Owen-Ball/LCR_Meter/CAD/menu_assembly/menu_assembly.SLDASM

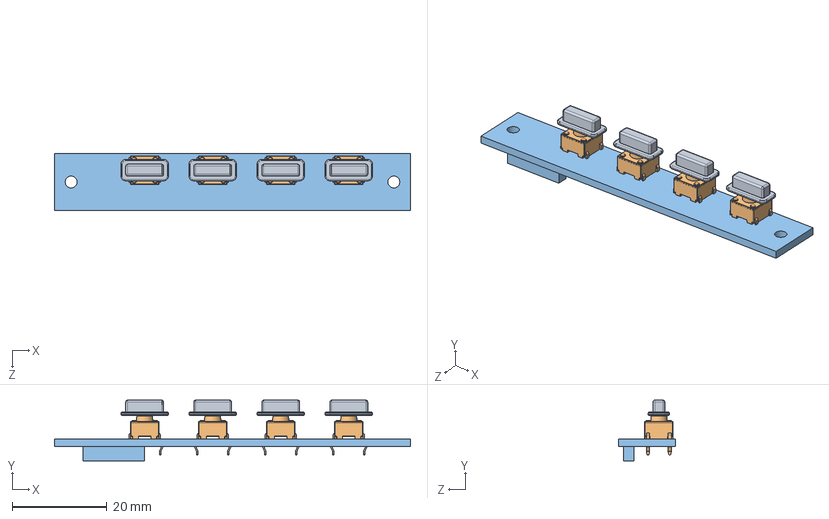
[picture p3: CAD file, 2026-08-15]
CAD/menu_assembly/menu_assembly.SLDASM
75.0 x 12.8 x 12.0 mm
menu_PCB
tactileswitch-short x 4
menu_buttons x 4
