Owen-Ball/LCR_Meter/CAD/selector_assembly/selector_assembly.SLDASM

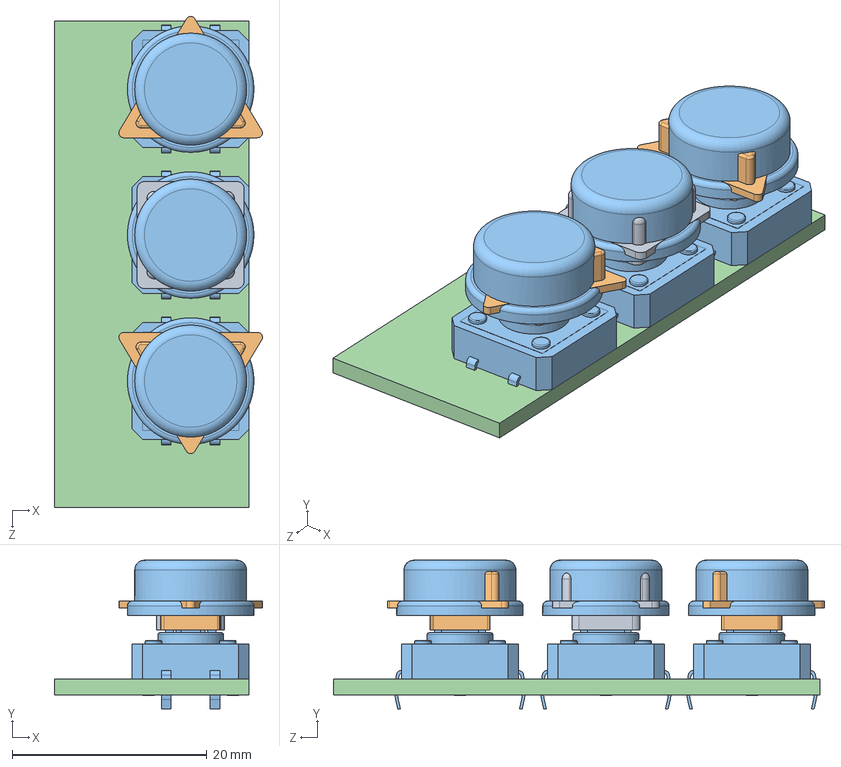
[picture p4: CAD file, 2026-09-21]
CAD/selector_assembly/selector_assembly.SLDASM
21.4 x 15.3 x 50.5 mm
pcb
button x 3
arrow_cap x 2
enter_cap
