Owen-Ball/LCR_Meter/CAD/m3_spacer.SLDPRT

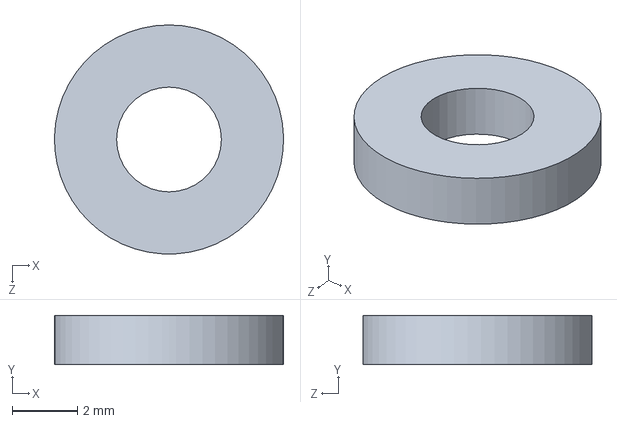
[picture p19: CAD file, 2026-09-24]
CAD/m3_spacer.SLDPRT
7.00 x 1.50 x 7.00 mm
