Owen-Ball/LCR_Meter/CAD/menu_assembly/tactileswitch-short.SLDPRT

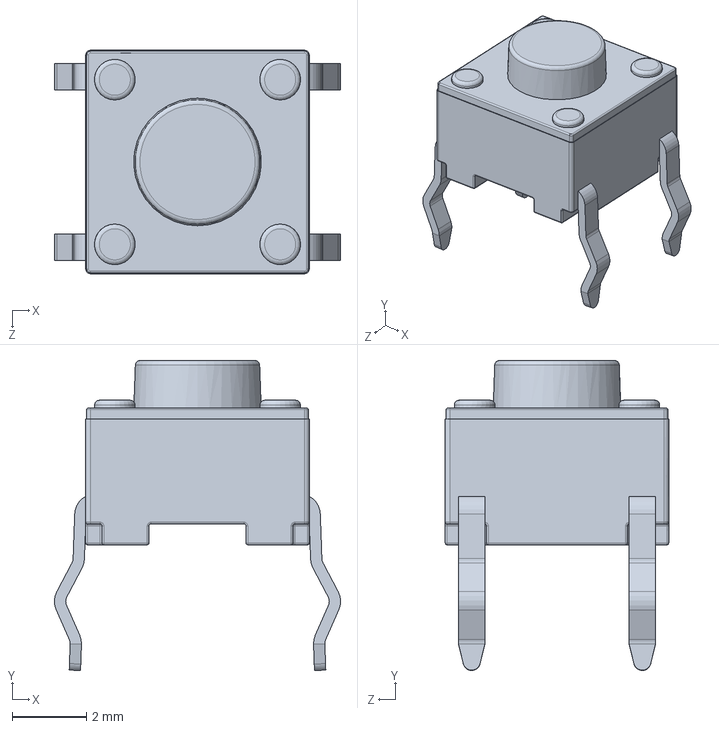
[picture p20: CAD file, 2026-08-01]
CAD/menu_assembly/tactileswitch-short.SLDPRT
7.69 x 8.33 x 6.01 mm
