Owen-Ball/LCR_Meter/CAD/selector_assembly/pcb.SLDPRT

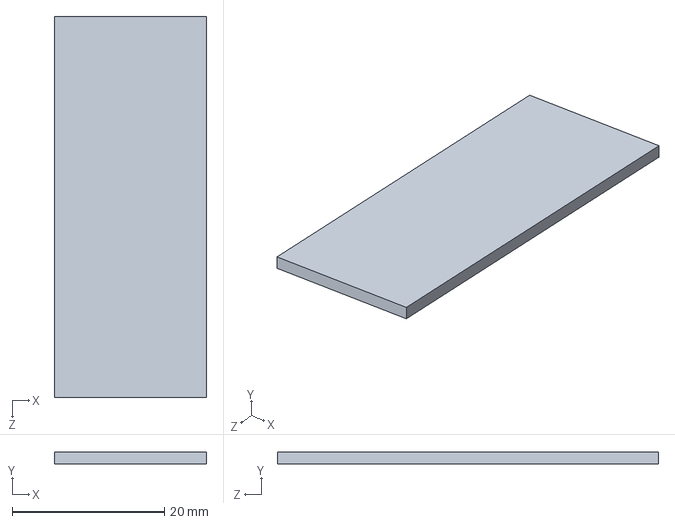
[picture p21: CAD file, 2026-08-11]
CAD/selector_assembly/pcb.SLDPRT
20.0 x 1.60 x 50.0 mm
