Owen-Ball/LCR_Meter/CAD/STLs/front_panel3.DXF

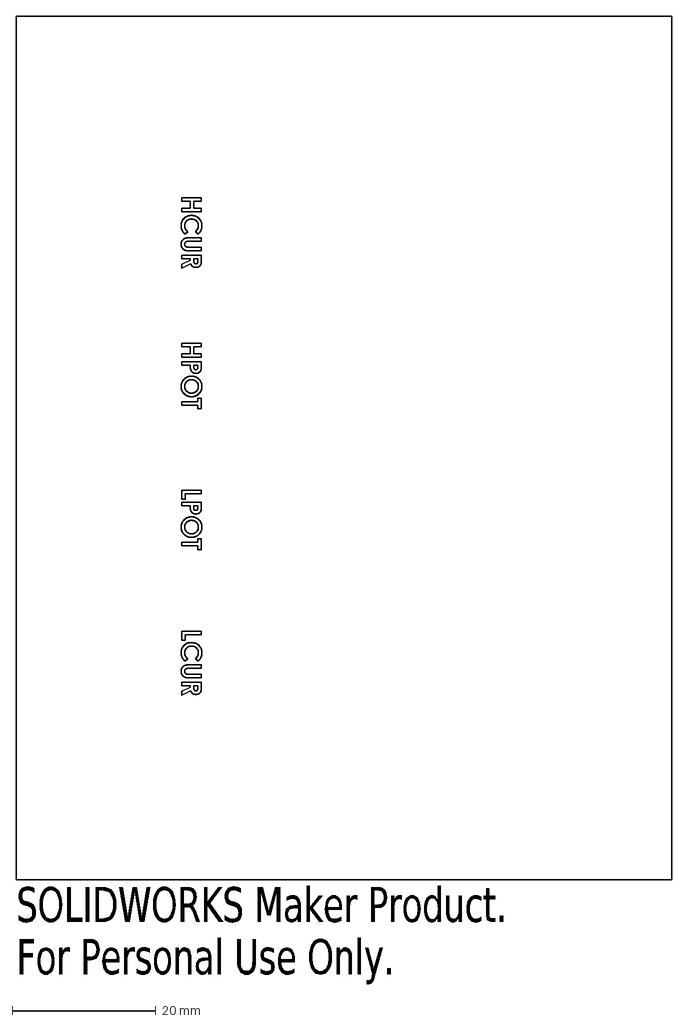
[picture p22: CAD file, 2026-09-24]
CAD/STLs/front_panel3.DXF
SOLIDWORKS Maker Product.
For Personal Use Only.
