Owen-Ball/LCR_Meter/CAD/compartment_lid.SLDPRT

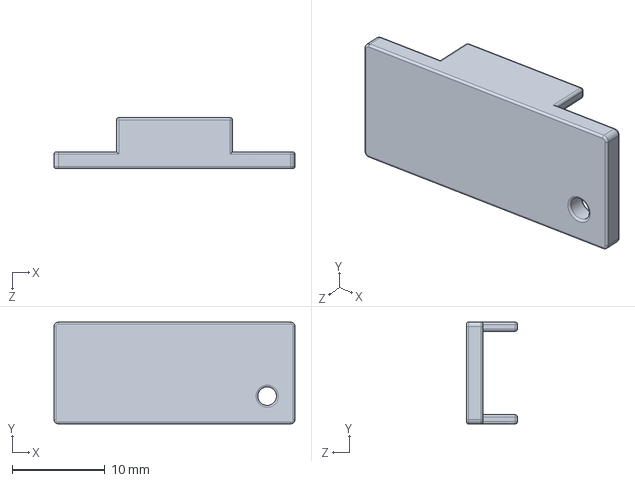
[picture p23: CAD file, 2026-09-24]
CAD/compartment_lid.SLDPRT
26.0 x 11.0 x 5.50 mm
