Owen-Ball/LCR_Meter/CAD/selector_assembly/button.SLDPRT

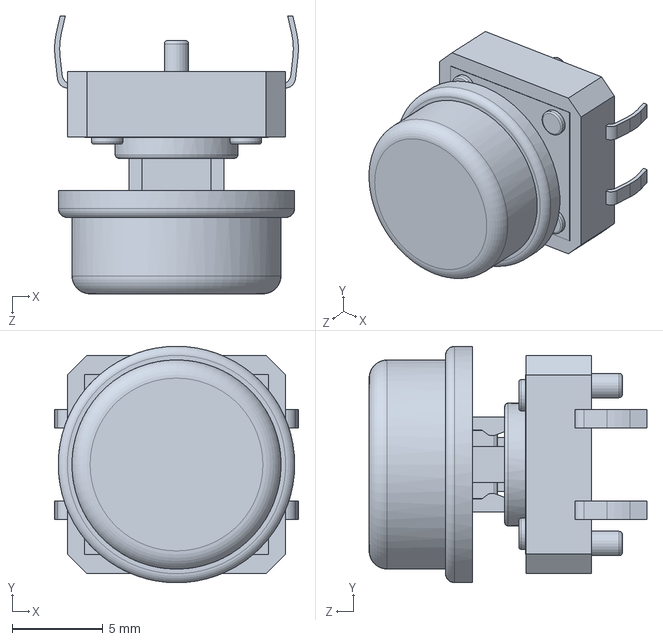
[picture p24: CAD file, 2026-08-02]
CAD/selector_assembly/button.SLDPRT
13.4 x 13.0 x 15.3 mm
