Owen-Ball/LCR_Meter/CAD/STLs/enter_cap - arrow_cap-1.STL

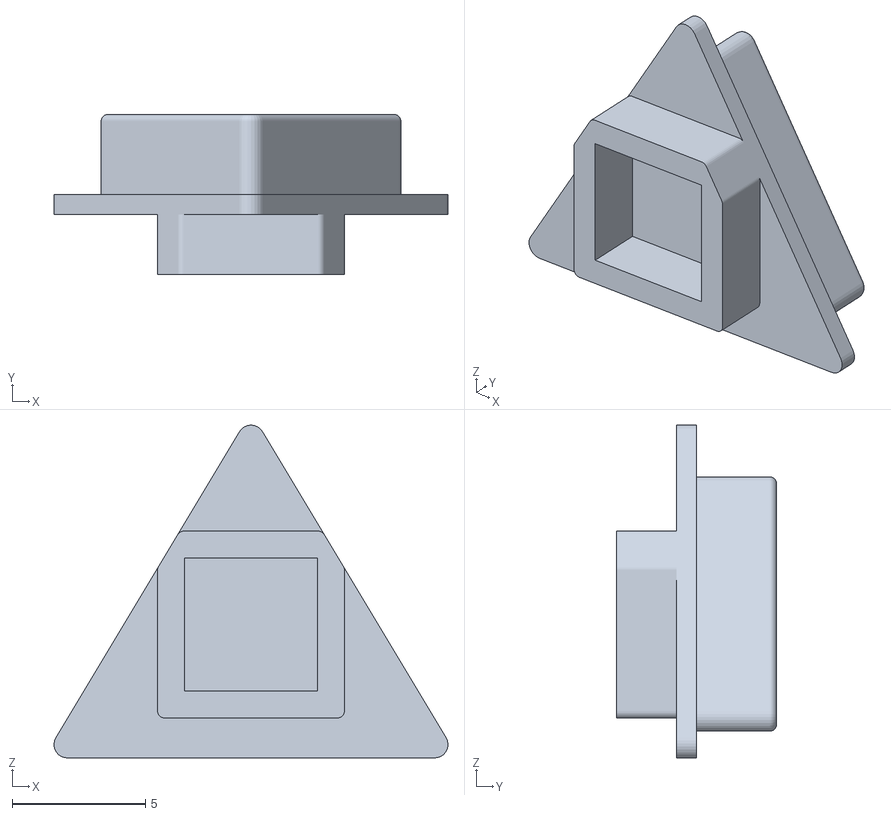
[picture p25: CAD file, 2026-09-21]
CAD/STLs/enter_cap - arrow_cap-1.STL
14.8 x 6.00 x 12.5
