Owen-Ball/LCR_Meter/CAD/STLs/enter_cap - button-1.STL

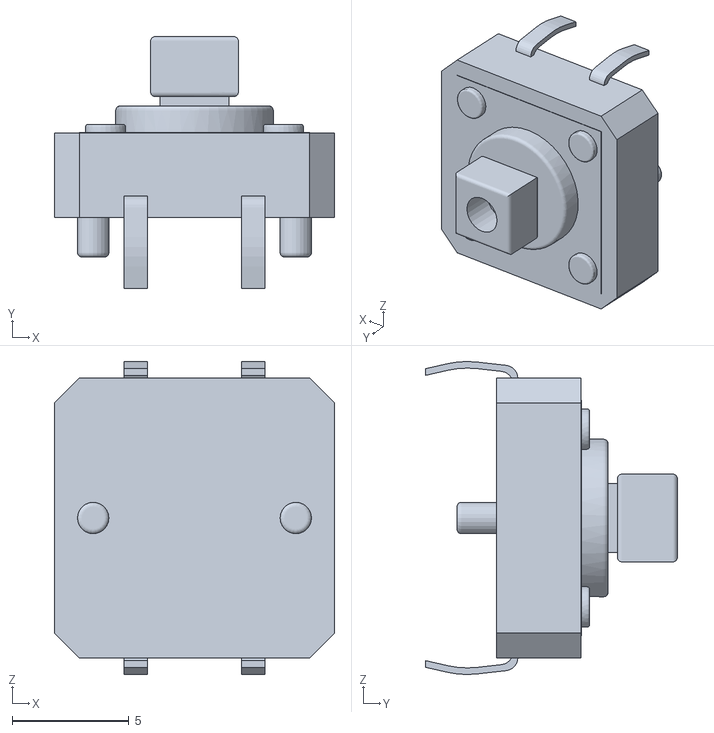
[picture p26: CAD file, 2026-09-21]
CAD/STLs/enter_cap - button-1.STL
12.0 x 10.8 x 13.4
