Owen-Ball/LCR_Meter/CAD/back_panel.SLDPRT

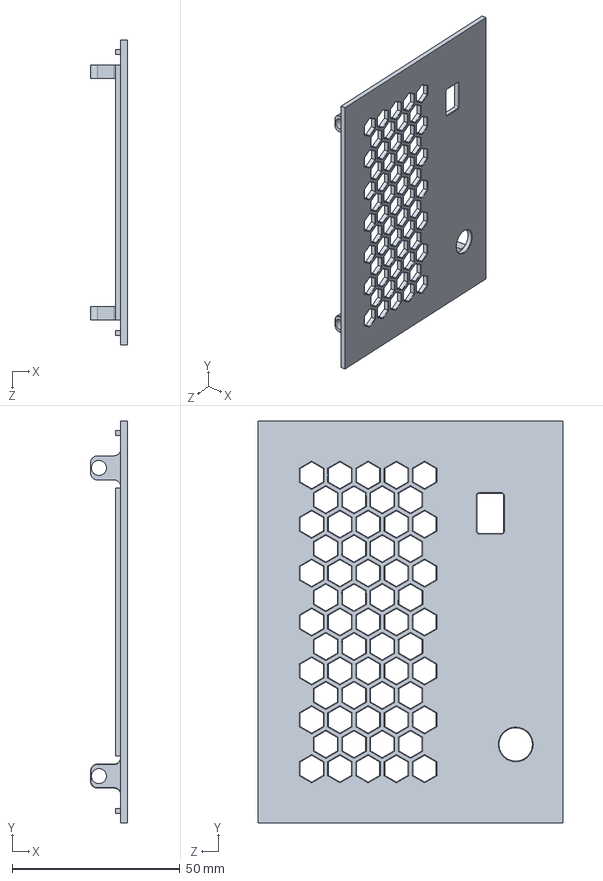
[picture p27: CAD file, 2026-09-18]
CAD/back_panel.SLDPRT
11.0 x 120.0 x 91.0 mm
