Owen-Ball/LCR_Meter/CAD/STLs/enter_cap - pcb-1.STL

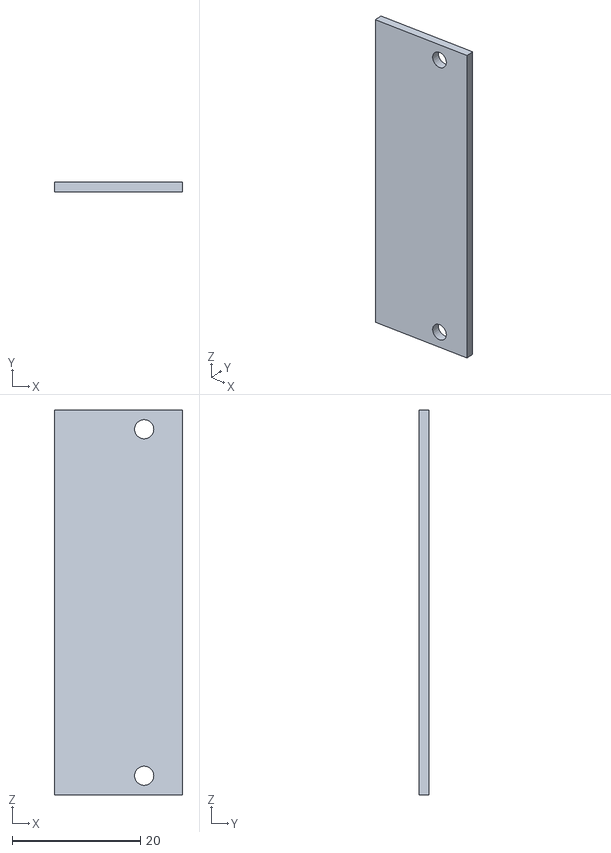
[picture p28: CAD file, 2026-09-21]
CAD/STLs/enter_cap - pcb-1.STL
20.0 x 1.60 x 60.0
