Owen-Ball/LCR_Meter/CAD/TFT_glass.SLDPRT

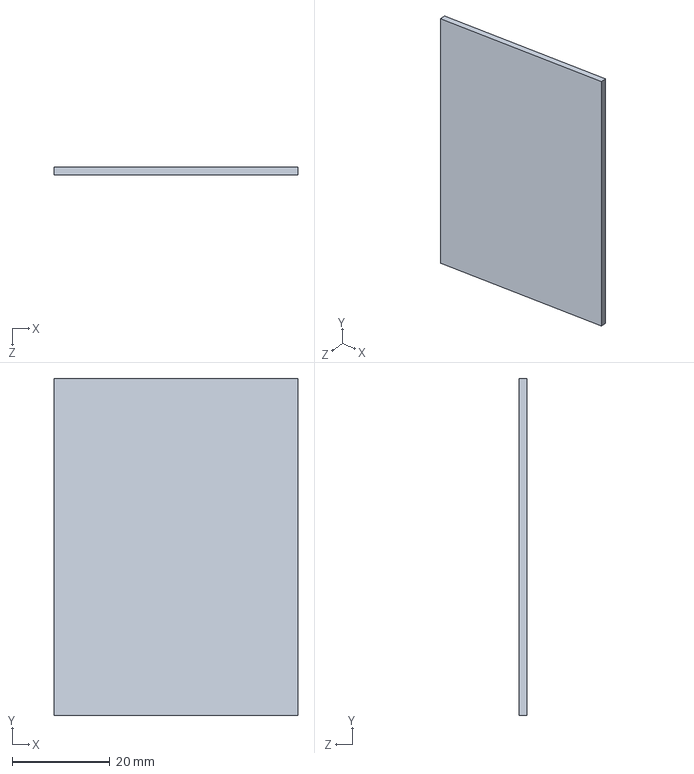
[picture p29: CAD file, 2026-08-01]
CAD/TFT_glass.SLDPRT
50.0 x 69.0 x 1.68 mm
