Owen-Ball/LCR_Meter/CAD/2.8 TFT Module.stp

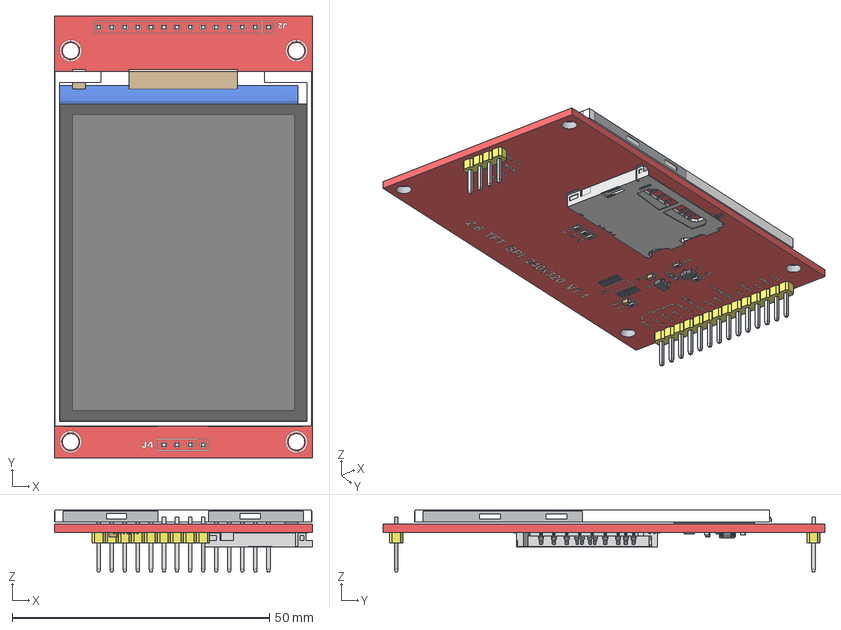
[picture p30: CAD file, 2026-08-01]
CAD/2.8 TFT Module.stp
50.2 x 85.9 x 12.0 mm
2.8 LCD TFT Module - Without Glass
0603 Resistor x 6
0603 Capacitor x 2
SOT23-3 x 2
2.8in TFT(Without Glass)- Tucked Cable
