Owen-Ball/LCR_Meter/CAD/TFT_2p8.step

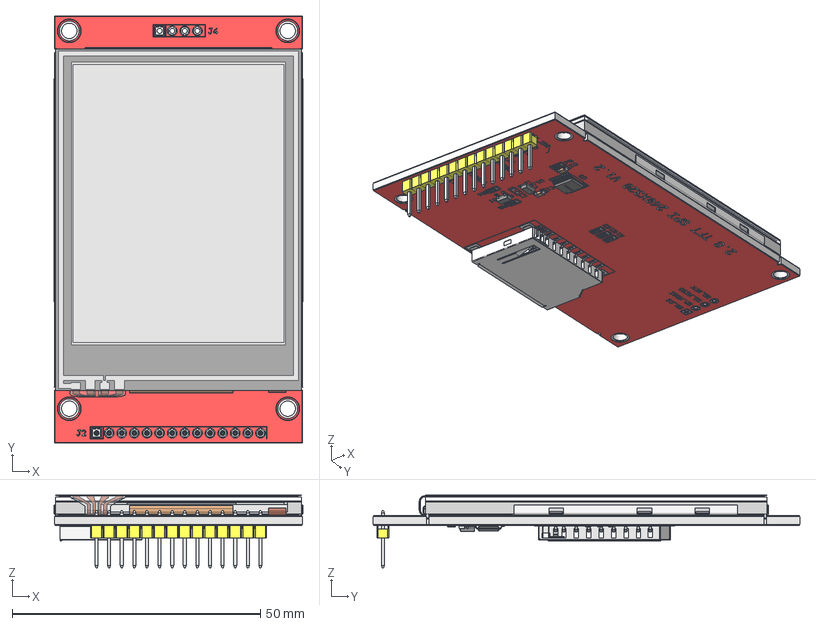
[picture p31: CAD file, 2026-07-29]
CAD/TFT_2p8.step
50.1 x 86.0 x 14.6 mm
plate and holes
circle001
circle002
circle003
circle004
border001
border002
ShapeString099
ShapeString100
ShapeString102
ShapeString103
cupper_upper
cupper_bottom
mask_bottom
res_silk
res_silk001
res_silk002
res_silk003
res_silk004
res_silk005
cap_silk_up
cap_silk_dwn
cap_silk_up001
cap_silk_dwn001
sot23_left
sot23_right
sot23_left001
sot23_right001
u2_silk002
sd_silk001
line_silk001
line_silk002
ShapeString067
ShapeString105
ShapeString106
ShapeString107
ShapeString108
ShapeString068
ShapeString110
ShapeString111
ShapeString112
ShapeString113
ShapeString069
ShapeString115
ShapeString116
ShapeString117
ShapeString070
ShapeString119
ShapeString120
ShapeString121
ShapeString122
ShapeString071
ShapeString124
ShapeString125
ShapeString126
ShapeString073
ShapeString128
ShapeString129
ShapeString130
ShapeString131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
