Owen-Ball/LCR_Meter/simulation/full_design/dac_filter.asc

C1: cap; 100p
C2: cap; 220p
C3: cap; 100p
R1: res; 10k
R2: res; 8.2k
R3: res; 10k
R4: res; 10k
R5: res; 10k
R6: res; 8.2k
U1: opamp2; tlv916x
Named nets: VCM, VP, VN, VOUT, VSS, VDD
