Owen-Ball/LCR_Meter/simulation/full_design/tb_dac_filter.asc

V1: voltage; SINE(0 1 50000); AC .61
V2: voltage; SINE(0 1 50000); AC .61
V3: voltage; 5
V4: voltage; 0
V5: voltage; 2.5
X1: dac_filter
Named nets: VCM, 0, VSS, VDD
.include tlv916x.txt
.ac dec 20 10 10Meg
