Owen-Ball/LCR_Meter/simulation/full_design/pga.asc

C1: cap; 470p
C2: cap; 470p
C3: cap; 2.7n
C4: cap; 100n
C5: cap; 2p
C6: cap; 2p
R1: res; 8.2k
R2: res; 1.6k
R3: res; 300
R4: res; 100
R5: res; 8.2k
R6: res; 1.6k
R7: res; 300
R8: res; 100
R9: res; 10Meg
R10: res; 10Meg
R11: res; 1k
R12: res; 1k
R13: res; 22
R14: res; 22
R15: res; 1k
R16: res; 1k
U1: THS4561
U2: ADG1209
U3: opamp2; OPA365
U4: opamp2; OPA365
Named nets: VDD, VSS, VP, VN, OUTP, OUTN, A0, A1, VCM
