Owen-Ball/LCR_Meter/simulation/full_design/top_hierarchy.asc

C1: cap; 1p
C2: cap; 1p
C3: cap; 100p
C4: cap; 15p
C5: cap; 50p
C6: cap; 15p
C7: cap; 15p
C8: cap; 100p
E1: e; 1
E2: e; 1
E3: e; 1
E4: e; 1
L1: ind; 1µ; Rser=1m
R1: res; 100
R2: res; 1k
R3: res; 10k
R4: res; 100k
R5: res; 100
R6: res; 1k
R7: res; 10k
R8: res; 100k
R9: res; 1k
R10: res; 10k
R11: res; 10k
U1: opamp2; tlv916x
U2: opamp2; tlv916x
U3: opamp2; tlv916x
U4: ADG709
V1: voltage; 5
V2: voltage; 0
V3: voltage; 2.3
V6: voltage; SINE(0 1 80000); AC 1
V7: voltage; SINE(0 1 80000); AC 1
V8: voltage; 0
V9: voltage; 5
X1: pga
X2: dac_filter
X3: pga
Named nets: 0, VSS, VDD, VCM, VMID, VMID2, RSEL0, RSEL1, TIA_OUT, TIA_FB, v_sns, i_sns, i_sns_pga, VSNS, v_sns_pga
.tran 0 .1m 0 10n
.include OPA365.txt
.ac dec 50 10 10Meg
.include tlv916x.txt
