Owen-Ball/LCR_Meter/simulation/diff_ac.asc

C1: cap; 2.7n
C3: cap; 470p
C4: cap; 470p
C5: cap; 1
C6: cap; 1
E1: e; 1
R1: res; 1k
R2: res; 1k
R3: res; 1.5k
R4: res; 1.5k
R5: res; 22
R6: res; 22
R7: res; 1Meg
R8: res; 1Meg
U1: THS4561
V1: voltage; ""; AC .5
V2: voltage; ""; AC .5
V3: voltage; 2.5
V4: voltage; 5
V5: voltage; ""; AC .5
V6: voltage; ""; AC .5
Named nets: VDDA, 0, i_dut2, VCM
.param R=1k VIN=1.25 R_diffin=1m
.ac dec 10 10 100Meg
