Owen-Ball/LCR_Meter/simulation/SigGen.asc

C1: cap; 220p
C2: cap; 220p
C3: cap; 470p
C4: cap; 1
C5: cap; 1
C6: cap; 10µ
C7: cap; 50p
C8: cap; 1µ
E1: e; 1
R1: res; 10k
R2: res; 10k
R3: res; 8.2k
R4: res; 8.2k
R5: res; 1Meg
R6: res; 1Meg
R7: res; 5.1k
R8: res; 5.1k
R9: res; 10k
R10: res; 10k
R11: res; 100
R12: res; 40
U1: opamp2; tlv916x
U2: opamp2; tlv916x
V1: voltage; 5
V2: voltage; 2.3
V3: voltage; SINE(0 .5 100); AC .5
V4: voltage; SINE(0 .5 100); AC .5
V5: voltage; ""; AC .5
V6: voltage; ""; AC .5
Named nets: 0, vdd, vcm, vout, vA, vB, vloop
.include tlv916x.txt
.ac dec 10 1 1G
.tran 0 100m 0 1u
