Owen-Ball/LCR_Meter/simulation/TIA_stab.asc

C1: cap; 30p
C2: cap; 1
C3: cap; 2p
C4: cap; 40p
C5: cap; 1p
C6: cap; 10p
C7: cap; 10p
E1: e; 1
R1: res; 1Meg
R2: res; 10k
R3: res; {R}
R4: res; 100k
R5: res; 1k
R6: res; 100
U1: opamp2; tlv916x
U2: ADG709
V1: voltage; 5
V2: voltage; 0
V3: voltage; ""; AC 1
V4: voltage; 2.5
V5: voltage; 5
V6: voltage; 0
Named nets: vss, vdd, 0, vcm, v0, v1
.ac dec 10 1 1G
.param R=10000
.include tlv916x.txt
