Owen-Ball/LCR_Meter/simulation/top.asc

C3: cap; 5n
C4: cap; 5n
C5: cap; 300p
C6: cap; 330p
E1: e; 1
E2: e; 1
E3: e; 1
E4: e; 1
L1: ind; 1e-6
R1: res; 100
R2: res; {2*R}
R3: res; {R}
R4: res; {R}
R5: res; 100
R7: res; {R}
R8: res; {R}
R9: res; {50*R}
R10: res; {R}
R11: res; {50*R}
R12: res; {R_diffin}
R13: res; {R_diffin}
R14: res; {R_diffin}
R15: res; {R_diffin}
R16: res; 1k
R17: res; 1k
R18: res; 500
R19: res; 500
R20: res; 30
R21: res; 30
R22: res; 1Meg
R: res; {2*R}
U1: opamp2; TLV354
U2: opamp2; TLV354
U3: opamp2; OPA365
U4: opamp2; OPA365
U5: opamp2; OPA365
U6: opamp2; OPA365
U7: THS4561
V1: voltage; SINE(0 {VIN} 50000)
V2: voltage; SINE(0 {VIN} 50000)
V3: voltage; 5
V4: voltage; 2.5
V5: voltage; 2.5
Named nets: 0, VDDA, VCM, vsig, vout, i_dut, v_dut, VN, i_dut2, v_dutraw
.include TLV354.txt 
.include OPA365.txt
.tran 0 100u 0 10n
.param R=1k VIN=1.25 R_diffin=1m
.options gmin=1e-10
.options gshunt=1e-9
.options reltol=0.01
.options abstol=1n
