Owen-Ball/LCR_Meter/simulation/Draft2.asc

C1: cap; 2p
C2: cap; 2p
C3: cap; 10p
C4: cap; 10p
C5: cap; 100m
C6: cap; 100m
E1: e; 1
E2: e; 100
R1: res; 27k
R3: res; 100Meg
R4: res; 5.1k
R5: res; 1k
R6: res; 330
R8: res; 100Meg
R9: res; 27k
R10: res; 5.1k
R11: res; 1k
R12: res; 330
R13: res; 1k
U1: opamp2; OPA365
U3: opamp2; OPA365
U4: MAX4052A
V1: voltage; 2.5
V2: voltage; SINE(0 .01 100000); AC 0
V3: voltage; 5
V4: voltage; 2.5
V5: voltage; 0; AC 1
V7: voltage; 2.5
V8: voltage; PULSE(0 .01 50u 1n 1n 50u 100u)
V9: voltage; 2.5
V10: voltage; 0; AC 1
Named nets: Vdd, 0, vout, vin, voutn, vinn, diff, diffin
.include OPA365.txt
.ac dec 10 10 100Meg
.tran 0 100u 0 10n
