Owen-Ball/LCR_Meter/simulation/TIA_transe.asc

C1: cap; 1p
C2: cap; 2p
C3: cap; 2p
C4: cap; 30p
E1: e; 1
E2: e; 1
R2: res; {R}
R3: res; {R}
U1: opamp2; tlv916x
V1: voltage; 2.5
V2: voltage; -2.5
V4: voltage; SINE(0 {VIN} {freq})
Named nets: vss, vdd, 0, VN, isns, VP, vsns
.include tlv916x.txt
.param R=100k VIN=1 freq=75000
.tran 0 10m 0 10n
