Owen-Ball/LCR_Meter/simulation/Draft1.asc

C1: cap; 5p
E1: e; 1
E2: e; 1
R1: res; 10k
R2: res; 1Meg
R3: res; 1Meg
R4: res; 27k
R5: res; 5.1k
R6: res; 1k
R7: res; 330
R8: res; 27k
R9: res; 5.1k
R10: res; 1k
R11: res; 330
U1: TMUX1309
U2: ADA4807-4
U4: ADG1209
U5: ADA4807-4
V1: voltage; SINE(3 1 100000)
V2: voltage; 3
V3: voltage; 2
V4: voltage; 1
V5: voltage; 4
V6: voltage; 3
V7: voltage; 2
V8: voltage; 1
V9: voltage; 5
V10: voltage; 2.5
V11: voltage; SINE(0 .01 10000)
Named nets: VDDA, 0, VN, vout, vin
.tran 0 100u 0 10n
.include OPA365.txt
