Owen-Ball/LCR_Meter/firmware/LCR/lcr_func.cpp

#include "lcr_func.h"
#include "calibration.h"
#include "codec.h"
#include "autorange.h"
#include "filter.h"

MovingAverage real_avg(16);
MovingAverage imag_avg(16);

float _curr_frequency;
float _curr_amplitude;

lcr_param_t primary_lcr_param;
lcr_param_t secondary_lcr_param;

bool auto_param;

float primary_lcr_value;
float secondary_lcr_value;

float resistance_lcr_value;
float reactance_lcr_value;

lcr_param_t *lcr_param_lookup[LCR_FUNC_NUM] = {
  &lcrParamRs,
  &lcrParamRp,
  &lcrParamCs,
  &lcrParamCp,
  &lcrParamLs,
  &lcrParamLp,
  &lcrParamXs,
  &lcrParamZMag,
  &lcrParamZPhase,
  &lcrParamQ,
  &lcrParamD,
};

void setLCRFrequency(float freq) {
  loadCalibrationPoint(freq);
  codecSetOutputFrequency(freq);
  resetAverageZ();
  _curr_frequency = freq;
}

void setLCRAmplitude(float amp) {
  float scaled_amp = amp / DAC_OUTPUT_VPP;
  scaled_amp = min(MAX_DAC_AMPLITUDE, scaled_amp); 
  codecSetOutputAmplitude(scaled_amp);
  _curr_amplitude = amp;
}

float getLCRFrequency() {
  return _curr_frequency;
}

float getLCRAmplitude() {
  return _curr_amplitude;
}

void setAverageZ(float count) {
  uint8_t width = round(count);
  real_avg.setWidth(width);
  imag_avg.setWidth(width);
}

void resetAverageZ() {
  real_avg.reset();
  imag_avg.reset();
}

Complex getAverageZ() {
  return Complex(real_avg.getAverage(), imag_avg.getAverage());  
}

void runAverageZ() {
  Complex Z = calculateZ();
  float mag = Z.modulus();
  float filt_mag = getAverageZ().modulus();

  if (mag / filt_mag < 1 / FILT_MAG_LIMIT || mag / filt_mag > FILT_MAG_LIMIT) {
    real_avg.reset();
    imag_avg.reset();
  }
  
  float R = Z.real();
  float X = Z.imag();

  real_avg.add(R);
  imag_avg.add(X);
}

void runAutoParam() {
  Complex Z = getAverageZ();
  float Q = getQ(Z, _curr_frequency);
  float X = getXs(Z, _curr_frequency);

  if (Q < 0.1) {
    primary_lcr_param = lcrParamRs;
    secondary_lcr_param = lcrParamQ;
  } else if (Q < 20 && X > 0) {
    primary_lcr_param = lcrParamLs;
    secondary_lcr_param = lcrParamRs;
  } else if (Q < 20 && X < 0) {
    primary_lcr_param = lcrParamCs;
    secondary_lcr_param = lcrParamRs;
  } else if (X > 0) {
    primary_lcr_param = lcrParamLp;
    secondary_lcr_param = lcrParamRp;
  } else if (X < 0) {
    primary_lcr_param = lcrParamCp;
    secondary_lcr_param = lcrParamRp;
  } else {
    primary_lcr_param = lcrParamCs;
    secondary_lcr_param = lcrParamRs;
  }
  
}

void runLCR() {
  codecAverageReadings();
  if (codecDataAvailable) {

    runAverageZ();

    Complex Z = getAverageZ();
    resistance_lcr_value = getRs_signed(Z, _curr_frequency);
    reactance_lcr_value = getXs(Z, _curr_frequency);

    if (getPhasorMag(Z, _curr_frequency) > Z_OVERFLOW) {
      primary_lcr_value = INFINITY;
      secondary_lcr_value = INFINITY;
    } else {
      if (auto_param) runAutoParam();
      primary_lcr_value = primary_lcr_param.value(Z, _curr_frequency);
      secondary_lcr_value = secondary_lcr_param.value(Z, _curr_frequency);
    }
    
    bool gain_ranged = gainAutorange(false);
    if (!gain_ranged) rangeAutorange(false);
    codecResetReadings();
  }
}

void setLCRParams(int index) {

  
  switch(index) {

    case 0:
      primary_lcr_param = lcrParamCs;
      secondary_lcr_param = lcrParamRs;
      auto_param = true;
      break;
    case 1:
      primary_lcr_param = lcrParamCs;
      secondary_lcr_param = lcrParamRs;
      auto_param = false;
      break;
    case 2:
      primary_lcr_param = lcrParamLs;
      secondary_lcr_param = lcrParamRs;
      auto_param = false;
      break;
    case 3:
      primary_lcr_param = lcrParamZMag;
      secondary_lcr_param = lcrParamZPhase;
      auto_param = false;
      break;
    default:
      primary_lcr_param = lcrParamCs;
      secondary_lcr_param = lcrParamRs;
      auto_param = false;
      break;
    
  }
}

void setLCRParams(float f) {
  int i = (int)round(f);
  setLCRParams(i);
}

Complex calculateZ() {
  Complex Z_meas = codecReadings.gain * calibration_data.tia_gain[board.getLCRRange()];
  return calibration_data.probe_Zp*Z_meas / (calibration_data.probe_Zp - Z_meas) - calibration_data.probe_Zs;
}

float getQ(Complex Z, float freq) {
  return abs(Z.imag() / Z.real());
}

float getD(Complex Z, float freq) {
  return abs(Z.real() / Z.imag());
}

float getPhasorAngle(Complex Z, float freq) {
  return Z.phase() * 180.0 / M_PI;
}

float getPhasorMag(Complex Z, float freq) {
  return Z.modulus();
}

float getRs(Complex Z, float freq) {
  return max(0, Z.real());
}

float getCs(Complex Z, float freq) {
  return max(0, -1 / (2*M_PI*freq*Z.imag()) );
}

float getLs(Complex Z, float freq) {
  return max(0, Z.imag() / (2*M_PI*freq) );
}

float getRp(Complex Z, float freq) {
  float q = getQ(Z, freq);
  return max(0, Z.real() * (q*q + 1));
}

float getCp(Complex Z, float freq) {
  float d = getD(Z, freq);
  return max(0, -1 / (Z.imag() * 2*M_PI*freq * (d*d + 1)));
}

float getLp(Complex Z, float freq) {
  float d = getD(Z, freq);
  return max(0, Z.imag() * (d*d + 1) / (2*M_PI*freq));
}

float getXs(Complex Z, float freq) {
  return Z.imag();
}

float getRs_signed(Complex Z, float freq) {
  return Z.real();
}


//Font Notes
//@= Ω
//& = μ
//[] = |Z|
//^ = °
//< = ∠

lcr_param_t lcrParamCs {
  .label = "Cs",
  .unit = "F",
  .min_exp = -12,
  .min_res = -13,
  .value = &getCs,
};

lcr_param_t lcrParamCp {
  .label = "Cp",
  .unit = "F",
  .min_exp = -12,
  .min_res = -13,
  .value = &getCp,
};

lcr_param_t lcrParamLs {
  .label = "Ls",
  .unit = "H",
  .min_exp = -6,
  .min_res = -8,
  .value = &getLs,
};

lcr_param_t lcrParamLp {
  .label = "Lp",
  .unit = "H",
  .min_exp = -6,
  .min_res = -8,
  .value = &getLp,
};

lcr_param_t lcrParamRs {
  .label = "Rs",
  .unit = "@",
  .min_exp = -3,
  .min_res = -4,
  .value = &getRs,
};

lcr_param_t lcrParamRp {
  .label = "Rp",
  .unit = "@",
  .min_exp = -3,
  .min_res = -4,
  .value = &getRp,
};

lcr_param_t lcrParamXs {
  .label = "Xs",
  .unit = "@",
  .min_exp = -3,
  .min_res = -4,
  .value = &getXs,
};

lcr_param_t lcrParamZMag {
  .label = "[]",
  .unit = "@",
  .min_exp = -3,
  .min_res = -4,
  .value = &getPhasorMag,
};

lcr_param_t lcrParamZPhase {
  .label = "<Z",
  .unit = "^",
  .min_exp = 0,
  .min_res = -2,
  .value = &getPhasorAngle,
};

lcr_param_t lcrParamD {
  .label = " D",
  .unit = "",
  .min_exp = 0,
  .min_res = -2,
  .value = &getD,
};

lcr_param_t lcrParamQ {
  .label = " Q",
  .unit = "",
  .min_exp = 0,
  .min_res = -2,
  .value = &getQ,
};
