Owen-Ball/LCR_Meter/firmware/LCR/images.h

#ifndef _IMAGES_
#define _IMAGES_


#define PROBE_BMP_WIDTH 25
#define PROBE_BMP_HEIGHT 50

//25x50px
const uint8_t clip_bmp[] PROGMEM = {
  0x04, 0x00, 0x08, 0x00, 0x04, 0x00, 0x08, 0x00, 0x0c, 0x00, 0x08, 0x00, 0x08, 0x00, 0x08, 0x00, 
  0x08, 0x00, 0x0c, 0x00, 0x18, 0x00, 0x04, 0x00, 0x10, 0x00, 0x04, 0x00, 0x10, 0x00, 0x04, 0x00, 
  0x3c, 0x00, 0x1e, 0x00, 0x3c, 0x00, 0x1e, 0x00, 0x7c, 0x00, 0x1f, 0x00, 0x7e, 0x00, 0x3f, 0x00, 
  0x7e, 0x00, 0x3f, 0x00, 0x7e, 0x00, 0x3f, 0x00, 0x7f, 0x00, 0x7f, 0x00, 0x7f, 0x00, 0x7f, 0x00, 
  0x3f, 0x00, 0x7e, 0x00, 0x3f, 0x80, 0xfe, 0x00, 0x3f, 0x80, 0xfe, 0x00, 0x3f, 0x80, 0xfe, 0x00, 
  0x3f, 0x80, 0xfe, 0x00, 0x1f, 0x80, 0xfc, 0x00, 0x1f, 0x80, 0xfc, 0x00, 0x1f, 0xc1, 0xfc, 0x00, 
  0x1f, 0xc1, 0xfc, 0x00, 0x0f, 0xc1, 0xf8, 0x00, 0x0f, 0xc1, 0xf8, 0x00, 0x07, 0xc1, 0xf0, 0x00, 
  0x07, 0xc1, 0xf0, 0x00, 0x03, 0xe3, 0xe0, 0x00, 0x03, 0xff, 0xe0, 0x00, 0x03, 0xff, 0xe0, 0x00, 
  0x03, 0xff, 0xe0, 0x00, 0x01, 0xff, 0xc0, 0x00, 0x01, 0xff, 0xc0, 0x00, 0x01, 0xff, 0xc0, 0x00, 
  0x00, 0xff, 0x80, 0x00, 0x00, 0xff, 0x80, 0x00, 0x00, 0x7f, 0x00, 0x00, 0x00, 0x3e, 0x00, 0x00, 
  0x00, 0x1c, 0x00, 0x00, 0x00, 0x1c, 0x00, 0x00, 0x00, 0x1c, 0x00, 0x00, 0x00, 0x08, 0x00, 0x00, 
  0x00, 0x08, 0x00, 0x00, 0x00, 0x08, 0x00, 0x00, 0x00, 0x08, 0x00, 0x00, 0x00, 0x08, 0x00, 0x00, 
  0x00, 0x08, 0x00, 0x00, 0x00, 0x08, 0x00, 0x00
};

const uint8_t tweezers_bmp[] PROGMEM = {
  0x00, 0x88, 0x00, 0x00, 0x00, 0x88, 0x00, 0x00, 0x00, 0x48, 0x00, 0x00, 0x00, 0x48, 0x00, 0x00, 
  0x00, 0x24, 0x00, 0x00, 0x00, 0x24, 0x00, 0x00, 0x00, 0x14, 0x00, 0x00, 0x00, 0x14, 0x00, 0x00, 
  0x00, 0x3e, 0x00, 0x00, 0x00, 0x3e, 0x00, 0x00, 0x00, 0x3e, 0x00, 0x00, 0x00, 0x3e, 0x00, 0x00, 
  0x00, 0x3e, 0x00, 0x00, 0x00, 0x3e, 0x00, 0x00, 0x00, 0x3e, 0x00, 0x00, 0x00, 0x7f, 0x00, 0x00, 
  0x00, 0x7f, 0x00, 0x00, 0x00, 0x7f, 0x00, 0x00, 0x00, 0x7f, 0x00, 0x00, 0x00, 0x7f, 0x00, 0x00, 
  0x00, 0x7f, 0x00, 0x00, 0x00, 0x77, 0x00, 0x00, 0x00, 0x77, 0x00, 0x00, 0x00, 0x77, 0x00, 0x00, 
  0x00, 0xe3, 0x80, 0x00, 0x00, 0xe3, 0x80, 0x00, 0x00, 0xe3, 0x80, 0x00, 0x00, 0xe3, 0x80, 0x00, 
  0x00, 0xe3, 0x80, 0x00, 0x00, 0xc1, 0x80, 0x00, 0x00, 0xc1, 0x80, 0x00, 0x00, 0xc1, 0x80, 0x00, 
  0x00, 0xc1, 0x80, 0x00, 0x00, 0xc1, 0x80, 0x00, 0x00, 0xc1, 0x80, 0x00, 0x01, 0xc1, 0xc0, 0x00, 
  0x01, 0x80, 0xc0, 0x00, 0x01, 0x80, 0xc0, 0x00, 0x01, 0x80, 0xc0, 0x00, 0x01, 0x80, 0xc0, 0x00, 
  0x01, 0x80, 0xc0, 0x00, 0x01, 0x80, 0xc0, 0x00, 0x01, 0x80, 0xc0, 0x00, 0x01, 0x80, 0xc0, 0x00, 
  0x01, 0x80, 0xc0, 0x00, 0x01, 0x80, 0xc0, 0x00, 0x00, 0x80, 0x80, 0x00, 0x00, 0x80, 0x80, 0x00, 
  0x00, 0x41, 0x00, 0x00, 0x00, 0x41, 0x00, 0x00
};

#endif
