Owen-Ball/LCR_Meter/firmware/LCR/selector.cpp

#include "selector.h"

void Selector::init(float min_val, float max_val, float init_val) {
    this->min_val = min_val;
    this->max_val = max_val;
    this->val = init_val;
    this->increment = 1.0f;
}

void Selector::setIncrement(float increment) {
    this->increment = increment;
}

float Selector::getIncrement() {
  return increment;
}

void Selector::incrementUp() {
    val += increment;
    if (val > max_val) val = max_val;
}

void Selector::incrementDown() {
    val -= increment;
    if (val < min_val) val = min_val;
}

float Selector::getValue() {
    return val;
}
