Owen-Ball/LCR_Meter/firmware/LCR/menubar.h

#ifndef _MENUBAR_
#define _MENUBAR_

#include <Arduino.h>
#include "SPI.h"
#include "ILI9341_t3n.h"
#include <XPT2046_Touchscreen.h>


#define MAX_CATEGORIES  8
#define MAX_ITEMS       8



typedef struct menu_item_struct {
  char display_text[16];
  float value;
  void (*func)(float f);
} menu_item_t;




class MenuBar {
  
  public:
    void init(uint16_t screen_width, uint16_t screen_height, uint16_t category_height, uint16_t item_height);
    void configColors(uint16_t text_color, uint16_t category_color, uint16_t item_color, uint16_t item_selected_color, uint16_t border_color);
    
    //Add caterogy. Up to 8
    void addCategory(const char *text, void (*func)(float f) = nullptr, float val = 0.0f, bool show_selection = true, bool initial_hover = true);

    uint8_t getCategoriesCount();
    
    //Up to 8 items per category. Adds to most recently created category
    void addItem(const menu_item_t &item);
    void addItem(const char *text, void (*func)(float f), float val = 0.0f);

    //Either open or close the category
    //If a category if empty, attempting to toggle it will immediately attempt to execute the callback function for the category
    uint8_t toggleCategory(uint8_t category_index);

    uint8_t moveUp();
    uint8_t moveDown();
    uint8_t enter();

    //Select an item from the currently open category
    void executeItem(uint8_t cat_index, uint8_t item_index);
    void executeItem(uint8_t item_index);

    //Set the display text for the currently selected category
    void setSelectedText(const char *text);
    void setSelectedText(const char *text, uint8_t cat_index);

    void drawMenu(ILI9341_t3n &tft);

    uint8_t processTouch(uint16_t x, uint16_t y);

    
  private:
    
    uint16_t screen_width;
    uint16_t screen_height;

    uint16_t category_height;
    uint16_t item_height;
    
    uint8_t num_categories;

    //currently selected category
    int8_t category_selected;

    //stores index of currently selected item
    uint8_t item_hovered[MAX_CATEGORIES];
    uint8_t item_selected[MAX_CATEGORIES];
    char selected_text[MAX_CATEGORIES][16];

    uint8_t item_counts[MAX_CATEGORIES];
    
    char categories[MAX_CATEGORIES][16];
    menu_item_t items[MAX_CATEGORIES][MAX_ITEMS];

    void (*category_funcs[MAX_CATEGORIES])(float f);
    float category_vals[MAX_CATEGORIES];
    bool show_selections[MAX_CATEGORIES];
    bool initial_hovers[MAX_CATEGORIES];

    uint16_t text_color;
    uint16_t category_color;
    uint16_t item_color;
    uint16_t item_selected_color;
    uint16_t border_color;
    
};


#endif
